biswro2023/smartiecar/Roboterauto/Hinten.jpg

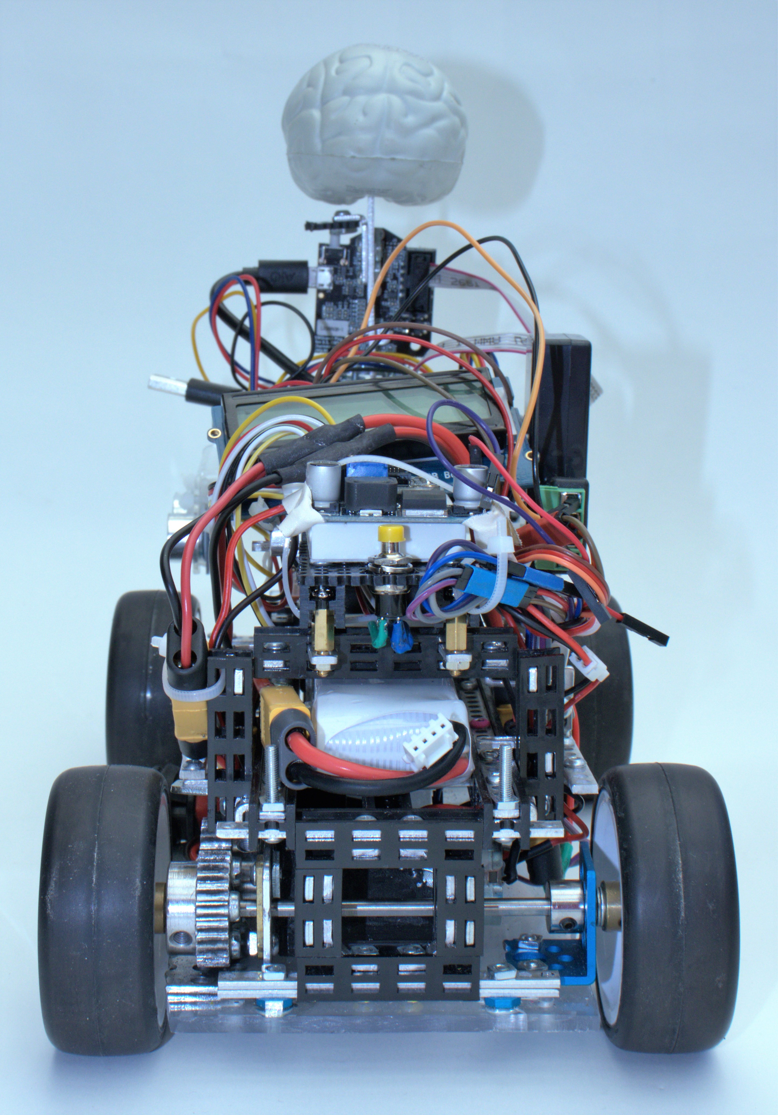
Roboterauto/Hinten.jpg
