biswro2023/smartiecar/Roboterauto/Rechts.jpg

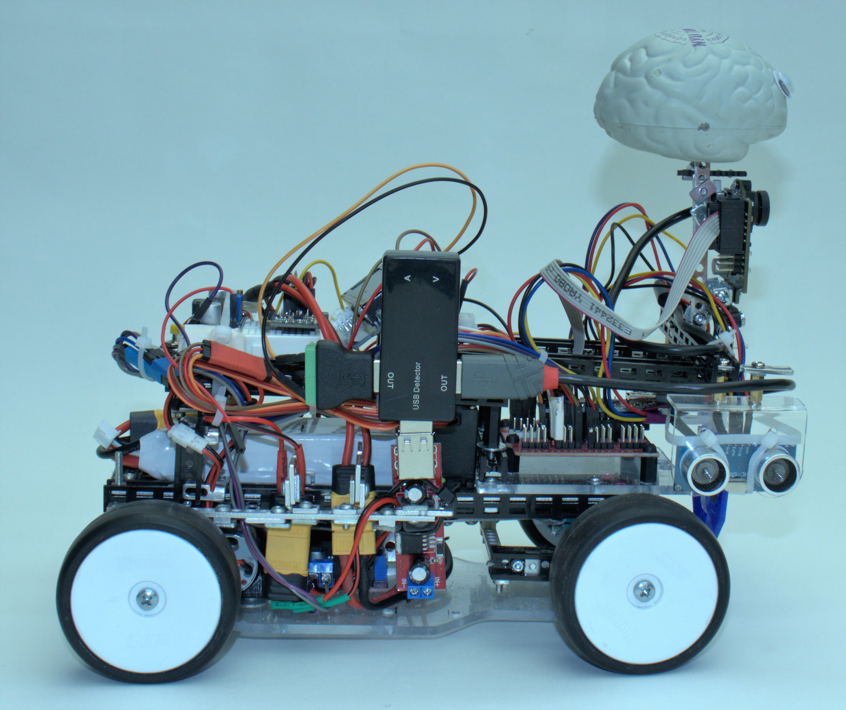
Roboterauto/Rechts.jpg
