biswro2023/smartiecar/Roboterauto/Unten.jpg

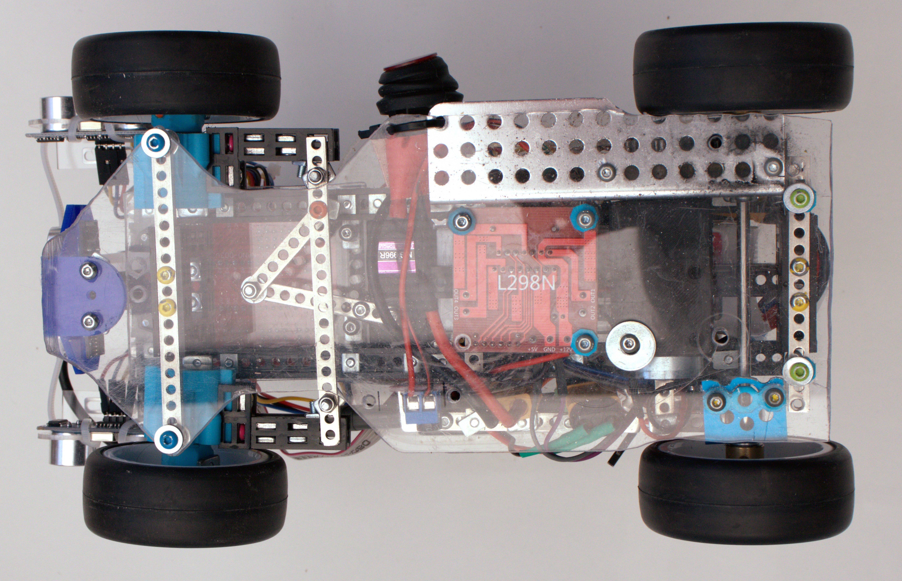
Roboterauto/Unten.jpg
