biswro2023/smartiecar/Roboterauto/Vorne.jpg

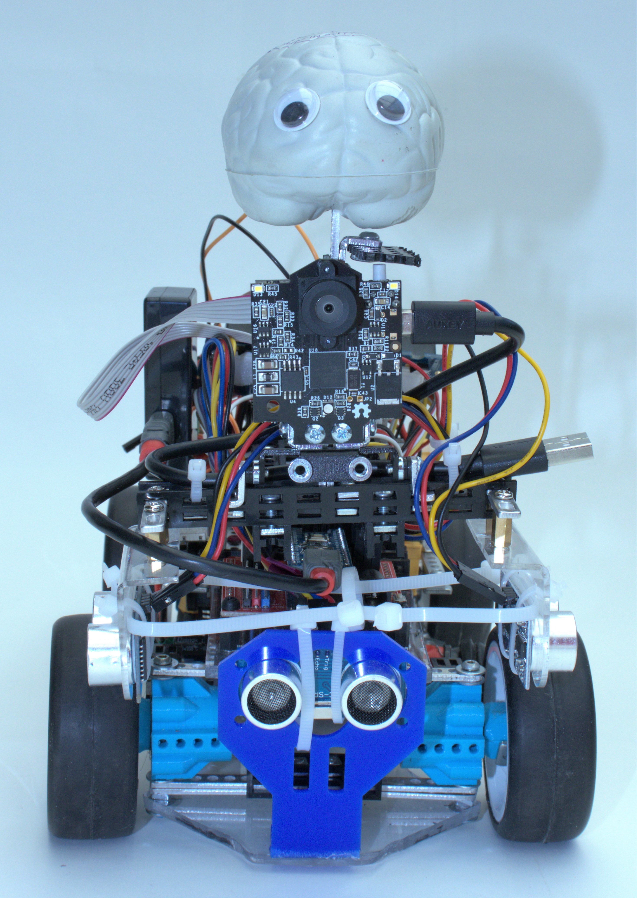
Roboterauto/Vorne.jpg
