biswro2023/smartiecar/Unser Team/Arduino peak version.png

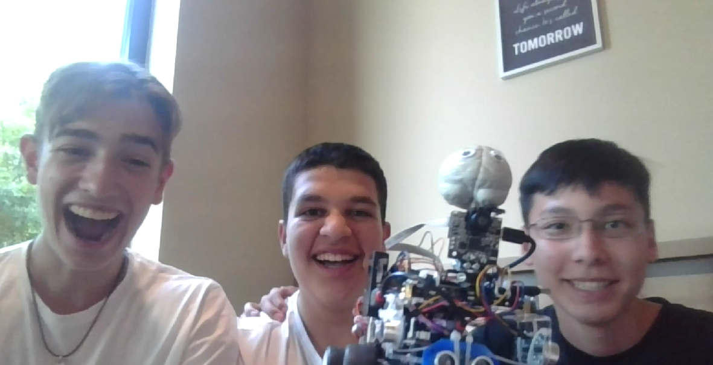
Unser Team/Arduino peak version.png
